MalcolmWilliams/Umbrella/PCB/Smart_Umbrella_Altium/Smart_Umbrella/Smart_Umbrella.pdf

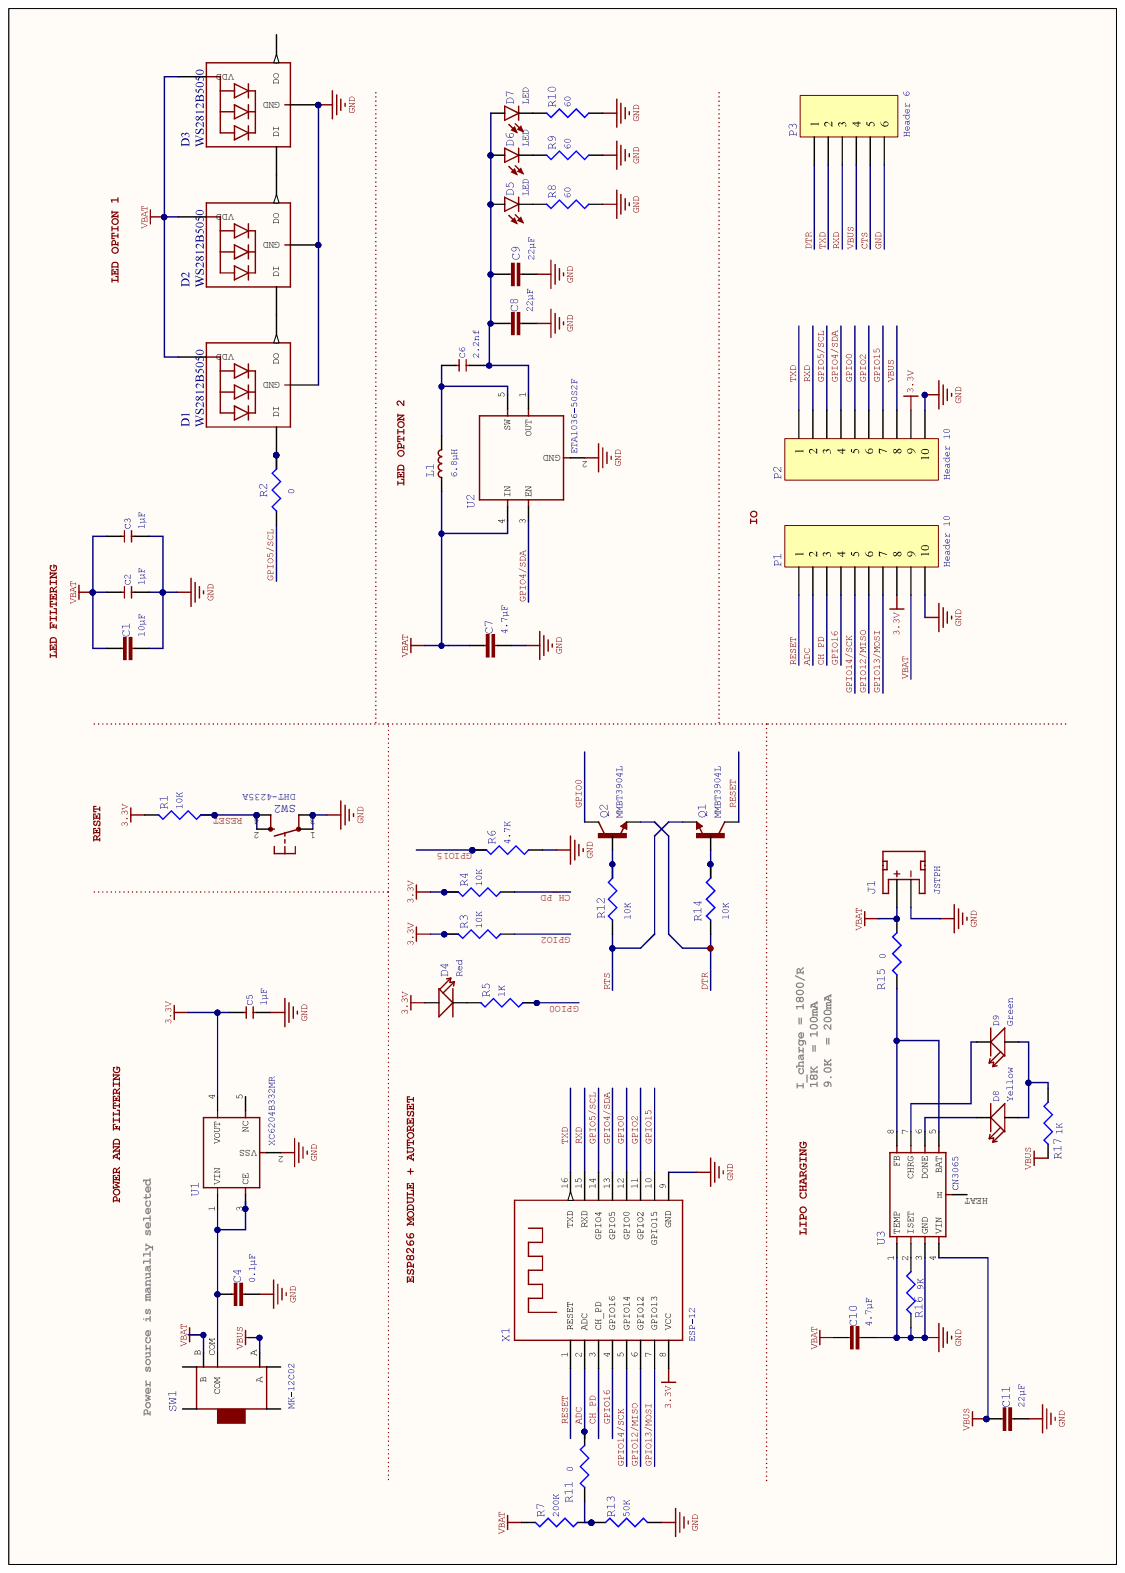
[picture p4: page 1]
RESET; GPIO15; GPIO0; GPIO2; VDD; GND; DHT-4235A; HEAT; VSS 2; GND 2
