MalcolmWilliams/Umbrella/src/BrightnessMap.h

int BrightnessMap[100] = {
  0  ,
15.05149978 ,
23.85606274 ,
30.10299957 ,
34.94850022 ,
38.90756252 ,
42.254902 ,
45.15449935 ,
47.71212547 ,
50  ,
52.06963426 ,
53.9590623  ,
55.69716762 ,
57.30640178 ,
58.80456295 ,
60.20599913 ,
61.52244607 ,
62.76362526 ,
63.93768005 ,
65.05149978 ,
66.11096474 ,
67.12113404 ,
68.0863918  ,
69.01056209 ,
69.89700043 ,
70.7486674  ,
71.56818821 ,
72.35790157 ,
73.11989989 ,
73.85606274 ,
74.56808469 ,
75.25749892 ,
75.92569699 ,
76.57394585 ,
77.20340222 ,
77.81512504 ,
78.4100862  ,
78.98917983 ,
79.55323035 ,
80.10299957 ,
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
};
